Pencreus/coin-vault/out/preview_lid.png

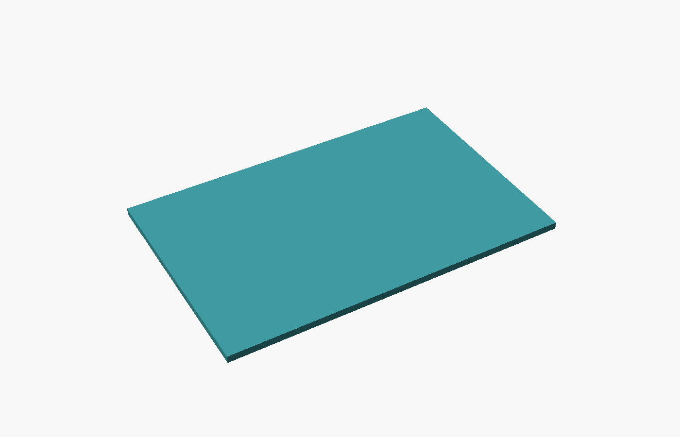
out/preview_lid.png
