Pencreus/coin-vault/out/preview_loaded_MIXED.png

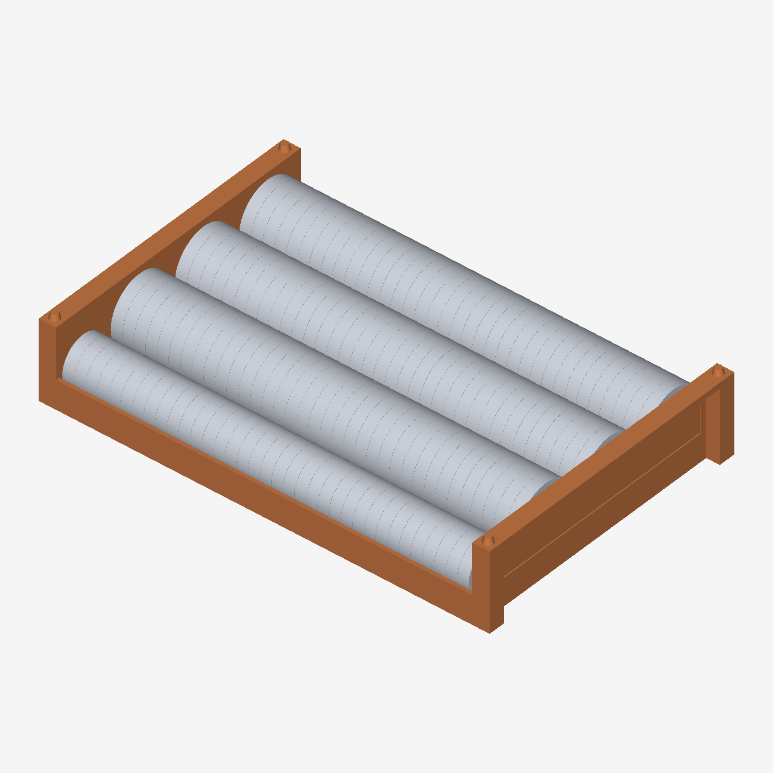
out/preview_loaded_MIXED.png
