Pencreus/coin-vault/out/preview_slab_on_5oz.png

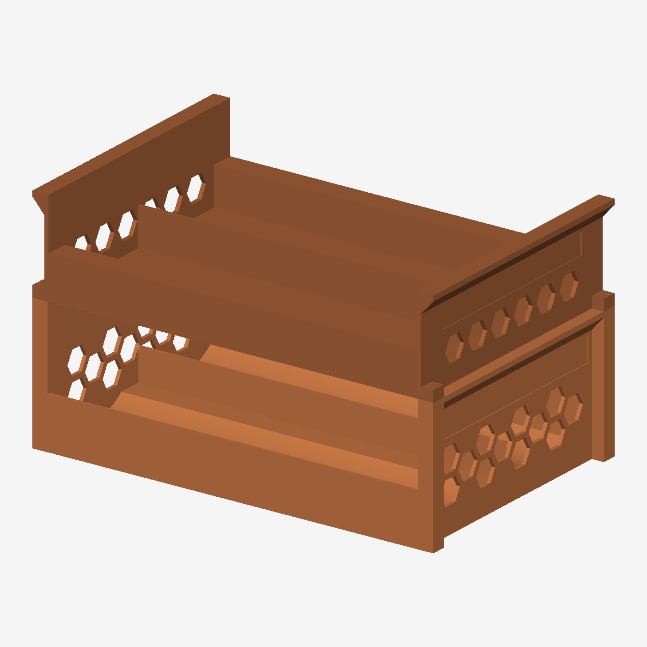
out/preview_slab_on_5oz.png
