Pencreus/coin-vault/out/preview_slab_tray.png

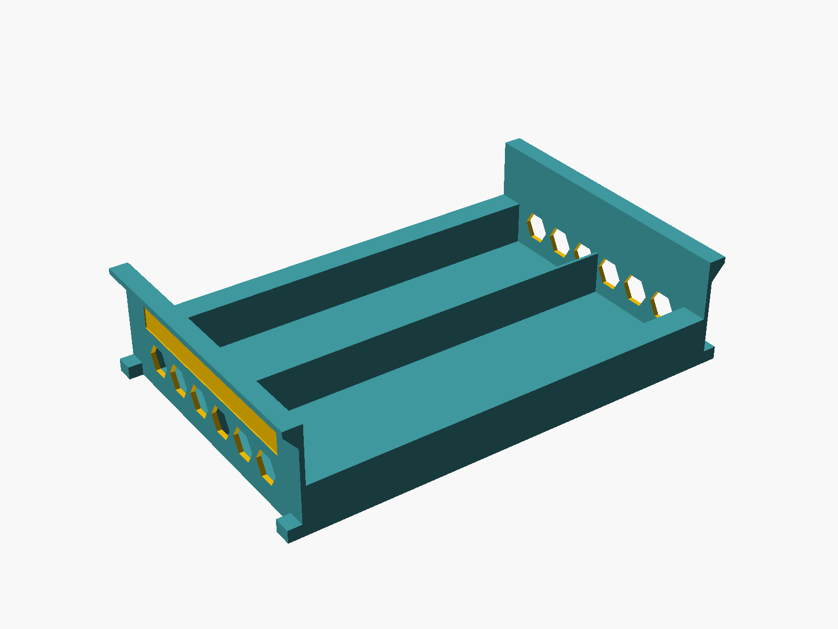
out/preview_slab_tray.png
