Pencreus/coin-vault/out/preview_stack_5oz_mixed_slab.png

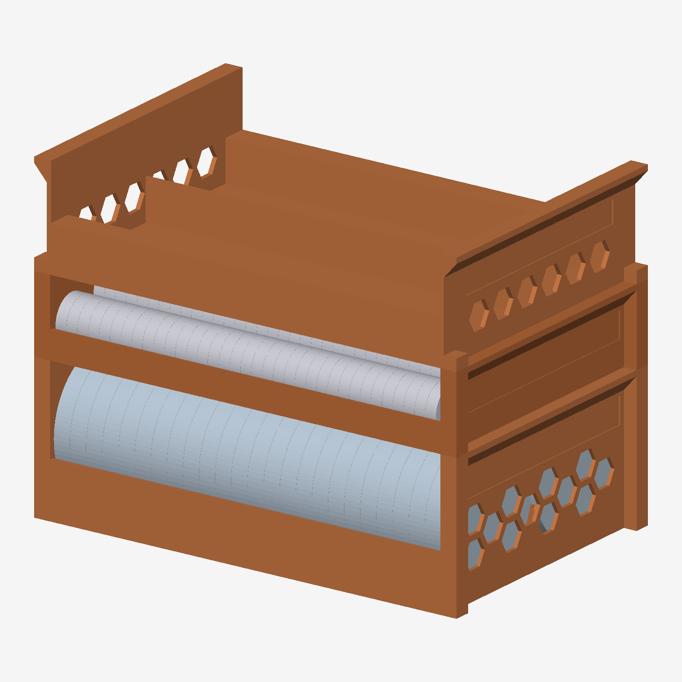
out/preview_stack_5oz_mixed_slab.png
