Pencreus/coin-vault/out/preview_stack_H39.png

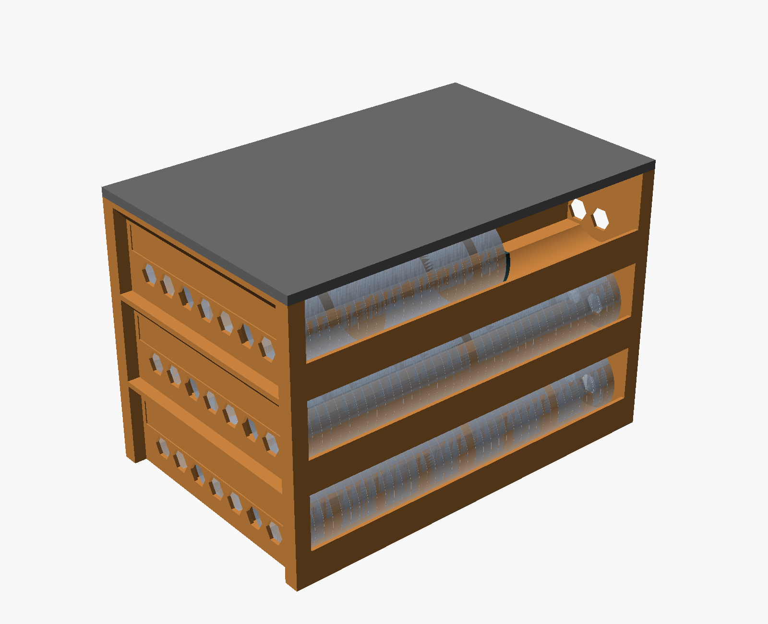
out/preview_stack_H39.png
