Pencreus/coin-vault/out/preview_stack_Y63.png

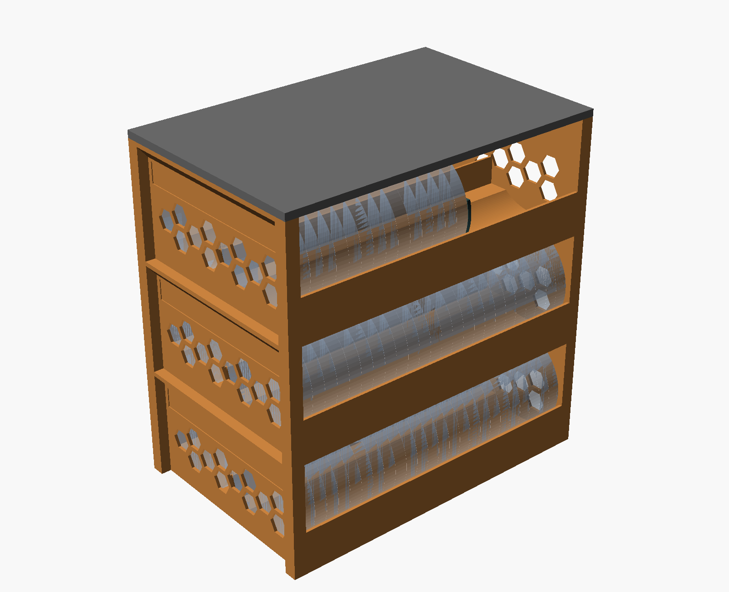
out/preview_stack_Y63.png
