Pencreus/coin-vault/out/preview_tray_HALF.png

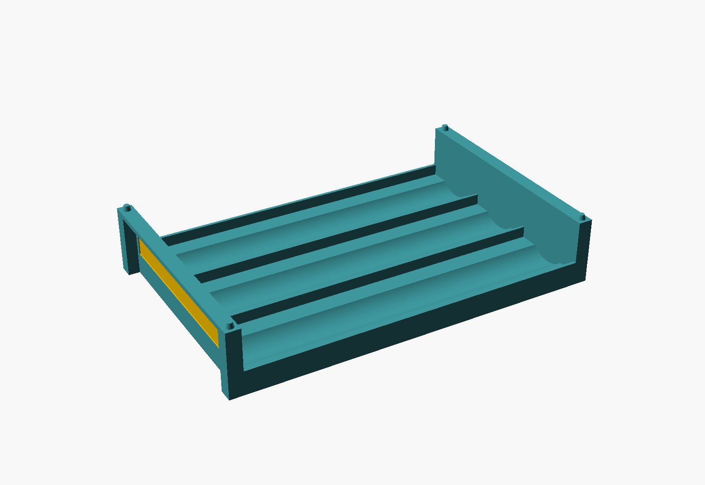
out/preview_tray_HALF.png
