Pencreus/coin-vault/out/preview_tray_Y63.png

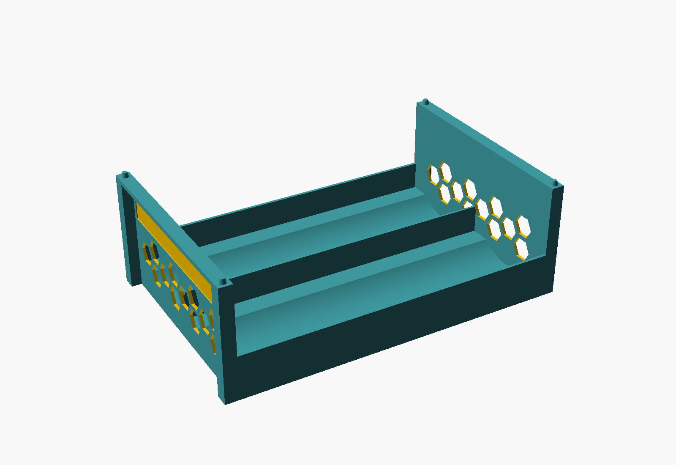
out/preview_tray_Y63.png
